obobed/flytboj/better-pelarboj/3D/bottom-view.png

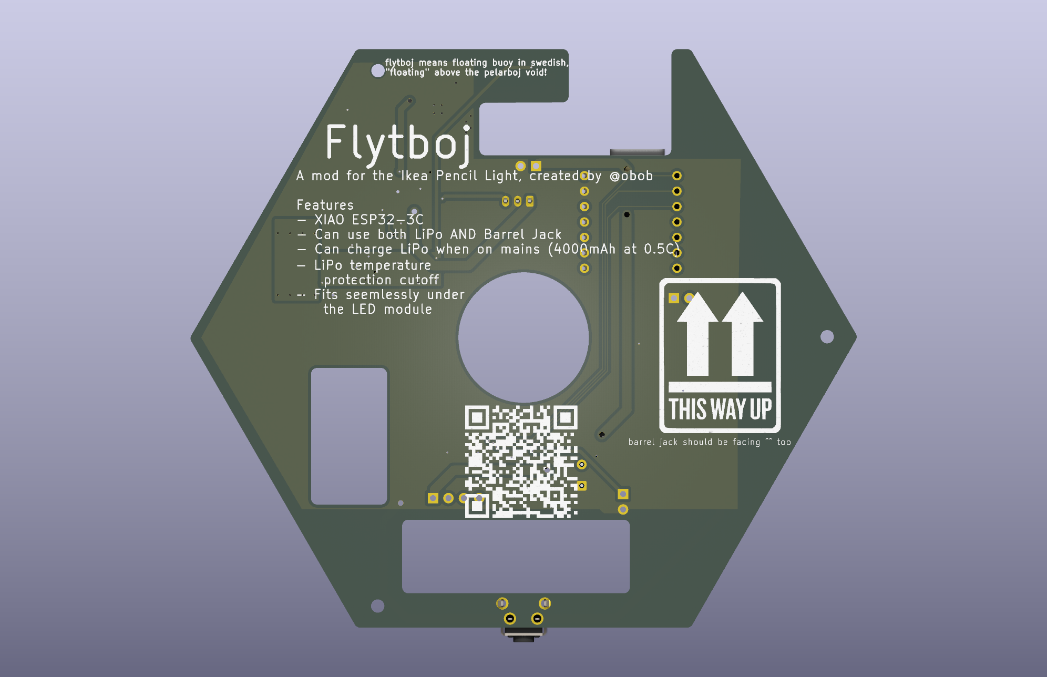
better-pelarboj/3D/bottom-view.png
