obobed/flytboj/better-pelarboj/3D/top-view.png

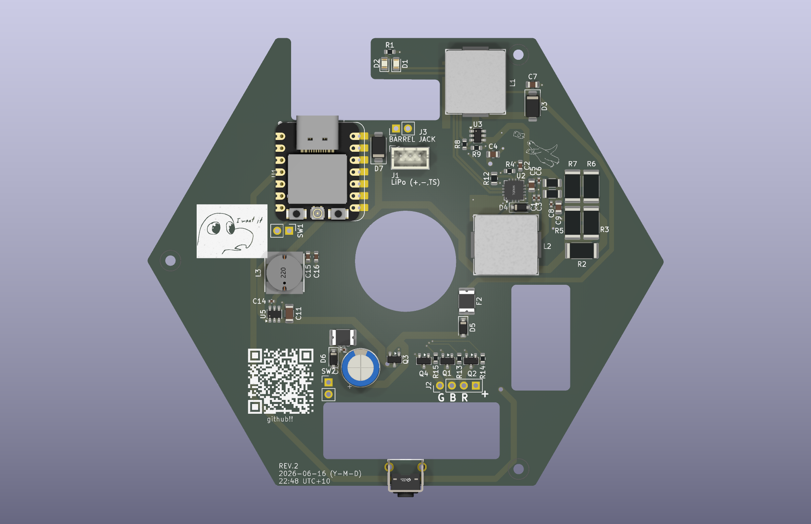
better-pelarboj/3D/top-view.png
