obobed/flytboj/plots/better-pelarboj.png

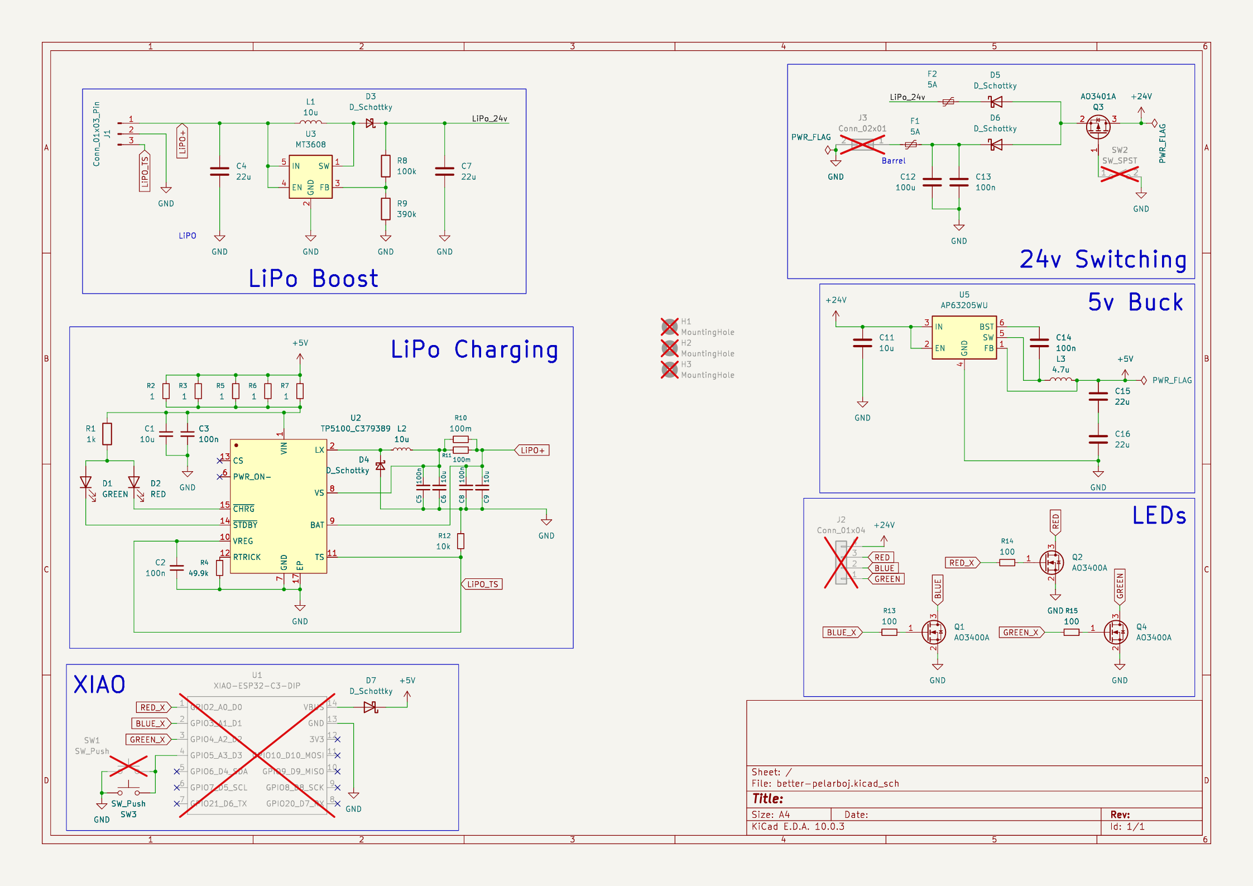
plots/better-pelarboj.png
