obobed/flytboj/rendering/render.png

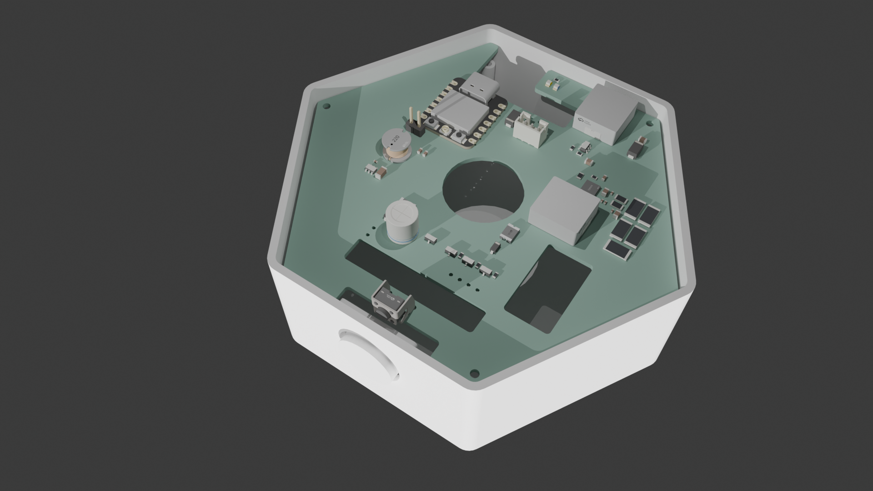
rendering/render.png
